mxmxmx/O_C/software/o_c_REV/APP_REFS.ino

// Copyright (c) 2016 Patrick Dowling, 2017 Max Stadler & Tim Churches
//
// Author: Patrick Dowling (pld@gurkenkiste.com)
// Enhancements: Max Stadler and Tim Churches
//
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
// Very simple "reference" voltage app (not so simple any more...)

#include "OC_apps.h"
#include "OC_menus.h"
#include "OC_strings.h"
#include "util/util_settings.h"
#include "OC_autotuner.h"
#include "src/drivers/FreqMeasure/OC_FreqMeasure.h"

// autotune constants:
#define FREQ_MEASURE_TIMEOUT 512
#define ERROR_TIMEOUT (FREQ_MEASURE_TIMEOUT << 0x4)
#define MAX_NUM_PASSES 1500
#define CONVERGE_PASSES 5
// 
static constexpr double kAaboveMidCtoC0 = 0.03716272234383494188492;

//
#ifdef FLIP_180
const uint8_t DAC_CHANNEL_FTM = DAC_CHANNEL_A;
#else
const uint8_t DAC_CHANNEL_FTM = DAC_CHANNEL_D;
#endif

// 
#ifdef BUCHLA_4U
  const float target_multipliers[OCTAVES] = { 1.0f, 2.0f, 4.0f, 8.0f, 16.0f, 32.0f, 64.0f, 128.0f, 256.0f, 512.0f };
#else
  const float target_multipliers[OCTAVES] = { 0.125f, 0.25f, 0.5f, 1.0f, 2.0f, 4.0f, 8.0f, 16.0f, 32.0f, 64.0f };
#endif

#ifdef BUCHLA_SUPPORT
  const float target_multipliers_1V2[OCTAVES] = {
    0.1767766952966368931843f,
    0.3149802624737182976666f,
    0.5612310241546865086093f,
    1.0f,
    1.7817974362806785482150f,
    3.1748021039363991668836f,
    5.6568542494923805818985f,
    10.0793683991589855253324f,
    17.9593927729499718282113f,
    32.0f
  };

  const float target_multipliers_2V0[OCTAVES] = {
    0.3535533905932737863687f,
    0.5f,
    0.7071067811865475727373f,
    1.0f,
    1.4142135623730951454746f,
    2.0f,
    2.8284271247461902909492f,
    4.0f,
    5.6568542494923805818985f,
    8.0f
  };
#endif

const uint8_t NUM_REF_CHANNELS = DAC_CHANNEL_LAST;

enum ReferenceSetting {
  REF_SETTING_OCTAVE,
  REF_SETTING_SEMI,
  REF_SETTING_RANGE,
  REF_SETTING_RATE,
  REF_SETTING_NOTES_OR_BPM,
  REF_SETTING_A_ABOVE_MID_C_INTEGER,
  REF_SETTING_A_ABOVE_MID_C_MANTISSA,
  REF_SETTING_PPQN,
  REF_SETTING_AUTOTUNE,
  REF_SETTING_DUMMY,
  REF_SETTING_LAST
};

enum ChannelPpqn {
  CHANNEL_PPQN_1,
  CHANNEL_PPQN_2,
  CHANNEL_PPQN_4,
  CHANNEL_PPQN_8,
  CHANNEL_PPQN_16,
  CHANNEL_PPQN_24,
  CHANNEL_PPQN_32,
  CHANNEL_PPQN_48,
  CHANNEL_PPQN_64,
  CHANNEL_PPQN_96,
  CHANNEL_PPQN_LAST
};

class ReferenceChannel : public settings::SettingsBase<ReferenceChannel, REF_SETTING_LAST> {
public:

  static constexpr size_t kHistoryDepth = 10;
  
  void Init(DAC_CHANNEL dac_channel) {
    InitDefaults();

    rate_phase_ = 0;
    mod_offset_ = 0;
    last_pitch_ = 0;
    autotuner_ = false;
    autotuner_step_ = OC::DAC_VOLT_0_ARM;
    dac_channel_ = dac_channel;
    auto_DAC_offset_error_ = 0;
    auto_frequency_ = 0;
    auto_last_frequency_ = 0;
    auto_freq_sum_ = 0;
    auto_freq_count_ = 0;
    auto_ready_ = 0;
    ticks_since_last_freq_ = 0;
    auto_next_step_ = false;
    autotune_completed_ = false;
    F_correction_factor_ = 0xFF;
    correction_direction_ = false;
    correction_cnt_positive_ = 0x0;
    correction_cnt_negative_ = 0x0;
    reset_calibration_data();
    update_enabled_settings();
    history_[0].Init(0x0);
  }

  int get_octave() const {
    return values_[REF_SETTING_OCTAVE];
  }

  int get_channel() const {
    return dac_channel_;
  }

  int32_t get_semitone() const {
    return values_[REF_SETTING_SEMI];
  }

  int get_range() const {
    return values_[REF_SETTING_RANGE];
  }

  uint32_t get_rate() const {
    return values_[REF_SETTING_RATE];
  }

  uint8_t get_notes_or_bpm() const {
    return values_[REF_SETTING_NOTES_OR_BPM];
  }

  double get_a_above_mid_c() const {
    double mantissa_divisor = 100.0;
    return static_cast<double>(values_[REF_SETTING_A_ABOVE_MID_C_INTEGER]) + (static_cast<double>(values_[REF_SETTING_A_ABOVE_MID_C_MANTISSA])/mantissa_divisor) ;
  }

  uint8_t get_a_above_mid_c_mantissa() const {
    return values_[REF_SETTING_A_ABOVE_MID_C_MANTISSA];
  }

  ChannelPpqn get_channel_ppqn() const {
    return static_cast<ChannelPpqn>(values_[REF_SETTING_PPQN]);
  }

  uint8_t autotuner_active() {
    return (autotuner_ && autotuner_step_) ? (dac_channel_ + 0x1) : 0x0;
  }

  bool autotuner_completed() {
    return autotune_completed_;
  }

  void autotuner_reset_completed() {
    autotune_completed_ = false;
  }

  bool autotuner_error() {
    return auto_error_;
  }

  uint8_t get_octave_cnt() {
    return octaves_cnt_ + 0x1;
  }

  uint8_t auto_tune_step() {
    return autotuner_step_;
  }

  void autotuner_arm(uint8_t _status) {
    reset_autotuner();
    autotuner_ = _status ? true : false;
  }
  
  void autotuner_run() {     
    autotuner_step_ = autotuner_ ? OC::DAC_VOLT_0_BASELINE : OC::DAC_VOLT_0_ARM;
    if (autotuner_step_ == OC::DAC_VOLT_0_BASELINE)
    // we start, so reset data to defaults:
      OC::DAC::set_default_channel_calibration_data(dac_channel_);
  }

  void auto_reset_step() {
    auto_num_passes_ = 0x0;
    auto_DAC_offset_error_ = 0x0;
    correction_direction_ = false;
    correction_cnt_positive_ = correction_cnt_negative_ = 0x0;
    F_correction_factor_ = 0xFF;
    auto_ready_ = false;
  }

  void reset_autotuner() {
    ticks_since_last_freq_ = 0x0;
    auto_frequency_ = 0x0;
    auto_last_frequency_ = 0x0;
    auto_error_ = 0x0;
    auto_ready_ = 0x0;
    autotuner_ = 0x0;
    autotuner_step_ = 0x0;
    F_correction_factor_ = 0xFF;
    correction_direction_ = false;
    correction_cnt_positive_ = 0x0;
    correction_cnt_negative_ = 0x0;
    octaves_cnt_ = 0x0;
    auto_num_passes_ = 0x0;
    auto_DAC_offset_error_ = 0x0;
    autotune_completed_ = 0x0;
    reset_calibration_data();
  }

  float get_auto_frequency() {
    return auto_frequency_;
  }

  uint8_t _ready() {
     return auto_ready_;
  }

  void reset_calibration_data() {
    
    for (int i = 0; i <= OCTAVES; i++) {
      auto_calibration_data_[i] = 0;
      auto_target_frequencies_[i] = 0.0f;
    }
  }

  uint8_t data_available() {
    return OC::DAC::calibration_data_used(dac_channel_);
  }

  void use_default() {
    OC::DAC::set_default_channel_calibration_data(dac_channel_);
  }

  void use_auto_calibration() {
    OC::DAC::set_auto_channel_calibration_data(dac_channel_);
  }
  
  bool auto_frequency() {

    bool _f_result = false;

    if (ticks_since_last_freq_ > ERROR_TIMEOUT) {
      auto_error_ = true;
    }
    
    if (FreqMeasure.available()) {
      
      auto_freq_sum_ = auto_freq_sum_ + FreqMeasure.read();
      auto_freq_count_ = auto_freq_count_ + 1;

      // take more time as we're converging toward the target frequency
      uint32_t _wait = (F_correction_factor_ == 0x1) ? (FREQ_MEASURE_TIMEOUT << 2) :  (FREQ_MEASURE_TIMEOUT >> 2);
  
      if (ticks_since_last_freq_ > _wait) {

        // store frequency, reset, and poke ui to preempt screensaver:
        auto_frequency_ = FreqMeasure.countToFrequency(auto_freq_sum_ / auto_freq_count_);
        history_[0].Push(auto_frequency_);
        auto_freq_sum_ = 0;
        auto_ready_ = true;
        auto_freq_count_ = 0;
        _f_result = true;
        ticks_since_last_freq_ = 0x0;
        OC::ui._Poke();
        for (auto &sh : history_)
          sh.Update();
      }
    }
    return _f_result;
  }

  void measure_frequency_and_calc_error() {

    switch(autotuner_step_) {

      case OC::DAC_VOLT_0_ARM:
      // do nothing
      break;
      case OC::DAC_VOLT_0_BASELINE:
      // 0V baseline / calibration point: in this case, we don't correct.
      {
        bool _update = auto_frequency();
        if (_update && auto_num_passes_ > kHistoryDepth) { 
          
          auto_last_frequency_ = auto_frequency_;
          float history[kHistoryDepth]; 
          float average = 0.0f;
          // average
          history_->Read(history);
          for (uint8_t i = 0; i < kHistoryDepth; i++)
            average += history[i];
          // ... and derive target frequency at 0V
          auto_frequency_ = (uint32_t) (0.5f + ((auto_frequency_ + average) / (float)(kHistoryDepth + 1))); // 0V 
          // reset step, and proceed:
          auto_reset_step();
          autotuner_step_++;
        }
        else if (_update) 
          auto_num_passes_++;
      }
      break;
      case OC::DAC_VOLT_TARGET_FREQUENCIES: 
      {
        #ifdef BUCHLA_SUPPORT
        
          switch(OC::DAC::get_voltage_scaling(dac_channel_)) {
            
            case VOLTAGE_SCALING_1_2V_PER_OCT: // 1.2V/octave
            auto_target_frequencies_[octaves_cnt_]  =  auto_frequency_ * target_multipliers_1V2[octaves_cnt_];
            break;
            case VOLTAGE_SCALING_2V_PER_OCT: // 2V/octave
            auto_target_frequencies_[octaves_cnt_]  =  auto_frequency_ * target_multipliers_2V0[octaves_cnt_];
            break;
            default: // 1V/octave
            auto_target_frequencies_[octaves_cnt_]  =  auto_frequency_ * target_multipliers[octaves_cnt_]; 
            break;
          }
        #else
          auto_target_frequencies_[octaves_cnt_]  =  auto_frequency_ * target_multipliers[octaves_cnt_]; 
        #endif
        octaves_cnt_++;
        // go to next step, if done:
        if (octaves_cnt_ >= OCTAVES) {
          octaves_cnt_ = 0x0;
          autotuner_step_++;
        }
      }
      break;
      case OC::DAC_VOLT_3m:
      case OC::DAC_VOLT_2m:
      case OC::DAC_VOLT_1m: 
      case OC::DAC_VOLT_0:
      case OC::DAC_VOLT_1:
      case OC::DAC_VOLT_2:
      case OC::DAC_VOLT_3:
      case OC::DAC_VOLT_4:
      case OC::DAC_VOLT_5:
      case OC::DAC_VOLT_6:
      { 
        bool _update = auto_frequency();
        
        if (_update && (auto_num_passes_ > MAX_NUM_PASSES)) {  
          /* target frequency reached */
          
          if ((autotuner_step_ > OC::DAC_VOLT_2m) && (auto_last_frequency_ * 1.25f > auto_frequency_))
              auto_error_ = true; // throw error, if things don't seem to double ...
          // average:
          float history[kHistoryDepth]; 
          float average = 0.0f;
          history_->Read(history);
          for (uint8_t i = 0; i < kHistoryDepth; i++)
            average += history[i];
          // store last frequency:
           auto_last_frequency_  = ((auto_frequency_ + average) / (float)(kHistoryDepth + 1));
          // and DAC correction value:
          auto_calibration_data_[autotuner_step_ - OC::DAC_VOLT_3m] = auto_DAC_offset_error_;
          // and reset step:
          auto_reset_step();
          autotuner_step_++; 
        }
        // 
        else if (_update) {

          // count passes
          auto_num_passes_++;
          // and correct frequency
          if (auto_target_frequencies_[autotuner_step_ - OC::DAC_VOLT_3m] > auto_frequency_) {
            // update correction factor?
            if (!correction_direction_)
              F_correction_factor_ = (F_correction_factor_ >> 1) | 1u;
            correction_direction_ = true;
            
            auto_DAC_offset_error_ += F_correction_factor_;
            // we're converging -- count passes, so we can stop after x attempts:
            if (F_correction_factor_ == 0x1)
              correction_cnt_positive_++;
          }
          else if (auto_target_frequencies_[autotuner_step_ - OC::DAC_VOLT_3m] < auto_frequency_) {
            // update correction factor?
            if (correction_direction_)
              F_correction_factor_ = (F_correction_factor_ >> 1) | 1u;
            correction_direction_ = false;
            
            auto_DAC_offset_error_ -= F_correction_factor_;
            // we're converging -- count passes, so we can stop after x attempts:
            if (F_correction_factor_ == 0x1)
              correction_cnt_negative_++;
          }

          // approaching target? if so, go to next step.
          if (correction_cnt_positive_ > CONVERGE_PASSES && correction_cnt_negative_ > CONVERGE_PASSES)
            auto_num_passes_ = MAX_NUM_PASSES << 1;
        }
      }
      break;
      case OC::AUTO_CALIBRATION_STEP_LAST:
      // step through the octaves:
      if (ticks_since_last_freq_ > 2000) {
        int32_t new_auto_calibration_point = OC::calibration_data.dac.calibrated_octaves[dac_channel_][octaves_cnt_] + auto_calibration_data_[octaves_cnt_];
        // write to DAC and update data
        if (new_auto_calibration_point >= 65536 || new_auto_calibration_point < 0) {
          auto_error_ = true;
          autotuner_step_++;
        }
        else {
          OC::DAC::set(dac_channel_, new_auto_calibration_point);
          OC::DAC::update_auto_channel_calibration_data(dac_channel_, octaves_cnt_, new_auto_calibration_point);
          ticks_since_last_freq_ = 0x0;
          octaves_cnt_++;
        }
      }
      // then stop ... 
      if (octaves_cnt_ > OCTAVES) { 
        autotune_completed_ = true;
        // and point to auto data ...
        OC::DAC::set_auto_channel_calibration_data(dac_channel_);
        autotuner_step_++;
      }
      break;
      default:
      autotuner_step_ = OC::DAC_VOLT_0_ARM;
      autotuner_ = 0x0;
      break;
    }
  }
  
  void autotune_updateDAC() {

    switch(autotuner_step_) {

      case OC::DAC_VOLT_0_ARM: 
      {
        F_correction_factor_ = 0x1; // don't go so fast
        auto_frequency();
        OC::DAC::set(dac_channel_, OC::calibration_data.dac.calibrated_octaves[dac_channel_][OC::DAC::kOctaveZero]);
      }
      break;
      case OC::DAC_VOLT_0_BASELINE:
      // set DAC to 0.000V, default calibration:
      OC::DAC::set(dac_channel_, OC::calibration_data.dac.calibrated_octaves[dac_channel_][OC::DAC::kOctaveZero]);
      break;
      case OC::DAC_VOLT_TARGET_FREQUENCIES:
      case OC::AUTO_CALIBRATION_STEP_LAST:
      // do nothing
      break;
      default: 
      // set DAC to calibration point + error
      {
        int32_t _default_calibration_point = OC::calibration_data.dac.calibrated_octaves[dac_channel_][autotuner_step_ - OC::DAC_VOLT_3m];
        OC::DAC::set(dac_channel_, _default_calibration_point + auto_DAC_offset_error_);
      }
      break;
    }
  }
 
  void Update() {

    if (autotuner_) {
      autotune_updateDAC();
      ticks_since_last_freq_++;
      return;
    }

    int octave = get_octave();
    int range = get_range();
    if (range) {
      rate_phase_ += OC_CORE_TIMER_RATE;
      if (rate_phase_ >= get_rate() * 1000000UL) {
        rate_phase_ = 0;
        mod_offset_ = 1 - mod_offset_;
      }
      octave += mod_offset_ * range;
    } else {
      rate_phase_ = 0;
      mod_offset_ = 0;
    }

    int32_t semitone = get_semitone();
    OC::DAC::set(dac_channel_, OC::DAC::semitone_to_scaled_voltage_dac(dac_channel_, semitone, octave, OC::DAC::get_voltage_scaling(dac_channel_)));
    last_pitch_ = (semitone + octave * 12) << 7;       
  }

  int num_enabled_settings() const {
    return num_enabled_settings_;
  }

  ReferenceSetting enabled_setting_at(int index) const {
    return enabled_settings_[index];
  }

  void update_enabled_settings() {
    ReferenceSetting *settings = enabled_settings_;
    *settings++ = REF_SETTING_OCTAVE;
    *settings++ = REF_SETTING_SEMI;
    *settings++ = REF_SETTING_RANGE;
    *settings++ = REF_SETTING_RATE;
    *settings++ = REF_SETTING_AUTOTUNE;
    //*settings++ = REF_SETTING_AUTOTUNE_ERROR;

    if (DAC_CHANNEL_FTM == dac_channel_) {
      *settings++ = REF_SETTING_NOTES_OR_BPM;
      *settings++ = REF_SETTING_A_ABOVE_MID_C_INTEGER;
      *settings++ = REF_SETTING_A_ABOVE_MID_C_MANTISSA;
      *settings++ = REF_SETTING_PPQN;
    }
    else {
      *settings++ = REF_SETTING_DUMMY;
      *settings++ = REF_SETTING_DUMMY;
    }
    
     num_enabled_settings_ = settings - enabled_settings_;
  }

  void RenderScreensaver(weegfx::coord_t start_x, uint8_t chan) const;

private:
  uint32_t rate_phase_;
  int mod_offset_;
  int32_t last_pitch_;
  bool autotuner_;
  uint8_t autotuner_step_;
  int32_t auto_DAC_offset_error_;
  float auto_frequency_;
  float auto_target_frequencies_[OCTAVES + 1];
  int16_t auto_calibration_data_[OCTAVES + 1];
  float auto_last_frequency_;
  bool auto_next_step_;
  bool auto_error_;
  bool auto_ready_;
  bool autotune_completed_;
  uint32_t auto_freq_sum_;
  uint32_t auto_freq_count_;
  uint32_t ticks_since_last_freq_;
  uint32_t auto_num_passes_;
  uint16_t F_correction_factor_;
  bool correction_direction_;
  int16_t correction_cnt_positive_;
  int16_t correction_cnt_negative_;
  int16_t octaves_cnt_;
  DAC_CHANNEL dac_channel_;

  OC::vfx::ScrollingHistory<float, kHistoryDepth> history_[0x1];

  int num_enabled_settings_;
  ReferenceSetting enabled_settings_[REF_SETTING_LAST];
};

const char* const notes_or_bpm[2] = {
 "notes",  "bpm", 
};

const char* const ppqn_labels[10] = {
 " 1",  " 2", " 4", " 8", "16", "24", "32", "48", "64", "96",  
};

const char* const error[] = {
  "0.050", "0.125", "0.250", "0.500", "1.000", "2.000", "4.000"
};

SETTINGS_DECLARE(ReferenceChannel, REF_SETTING_LAST) {
  #ifdef BUCHLA_4U
  { 0, 0, 9, "Octave", nullptr, settings::STORAGE_TYPE_I8 },
  #elif defined(VOR) 
  {0, 0, 10, "Octave", nullptr, settings::STORAGE_TYPE_I8 },
  #else
  { 0, -3, 6, "Octave", nullptr, settings::STORAGE_TYPE_I8 },
  #endif
  { 0, 0, 11, "Semitone", OC::Strings::note_names_unpadded, settings::STORAGE_TYPE_U8 },
  { 0, -3, 3, "Mod range oct", nullptr, settings::STORAGE_TYPE_U8 },
  { 0, 0, 30, "Mod rate (s)", nullptr, settings::STORAGE_TYPE_U8 },
  { 0, 0, 1, "Notes/BPM :", notes_or_bpm, settings::STORAGE_TYPE_U8 },
  { 440, 400, 480, "A above mid C", nullptr, settings::STORAGE_TYPE_U16 },
  { 0, 0, 99, " > mantissa", nullptr, settings::STORAGE_TYPE_U8 },
  { CHANNEL_PPQN_4, CHANNEL_PPQN_1, CHANNEL_PPQN_LAST - 1, "> ppqn", ppqn_labels, settings::STORAGE_TYPE_U8 },
  { 0, 0, 0, "--> autotune", NULL, settings::STORAGE_TYPE_U8 },
  { 0, 0, 0, "-", NULL, settings::STORAGE_TYPE_U8 } // dummy
};

class ReferencesApp {
public:
  ReferencesApp() { }
  
  OC::Autotuner<ReferenceChannel> autotuner;

  void Init() {
    int dac_channel = DAC_CHANNEL_A;
    for (auto &channel : channels_)
      channel.Init(static_cast<DAC_CHANNEL>(dac_channel++));

    ui.selected_channel = DAC_CHANNEL_FTM;
    ui.cursor.Init(0, channels_[DAC_CHANNEL_FTM].num_enabled_settings() - 1);

    freq_sum_ = 0;
    freq_count_ = 0;
    frequency_ = 0;
    autotuner.Init();
  }

  void ISR() {
      
    for (auto &channel : channels_)
      channel.Update();

    uint8_t _autotuner_active_channel = 0x0;
    for (auto &channel : channels_)
       _autotuner_active_channel += channel.autotuner_active();

    if (_autotuner_active_channel) {
      channels_[_autotuner_active_channel - 0x1].measure_frequency_and_calc_error();
      return;
    }
    else if (FreqMeasure.available()) {
      // average several readings together
      freq_sum_ = freq_sum_ + FreqMeasure.read();
      freq_count_ = freq_count_ + 1;
      
      if (milliseconds_since_last_freq_ > 750) {
        frequency_ = FreqMeasure.countToFrequency(freq_sum_ / freq_count_);
        freq_sum_ = 0;
        freq_count_ = 0;
        milliseconds_since_last_freq_ = 0;
       }
     } else if (milliseconds_since_last_freq_ > 100000) {
      frequency_ = 0.0f;
     }
  }

  ReferenceChannel &selected_channel() {
    return channels_[ui.selected_channel];
  }

  struct {
    int selected_channel;
    menu::ScreenCursor<menu::kScreenLines> cursor;
  } ui;

  ReferenceChannel channels_[DAC_CHANNEL_LAST];

  float get_frequency( ) {
    return(frequency_) ;
  }

  float get_ppqn() {
    float ppqn_ = 4.0 ;
    switch(channels_[DAC_CHANNEL_FTM].get_channel_ppqn()){
      case CHANNEL_PPQN_1:
        ppqn_ = 1.0;
        break;
      case CHANNEL_PPQN_2:
        ppqn_ = 2.0;
        break;
      case CHANNEL_PPQN_4:
        ppqn_ = 4.0;
        break;
      case CHANNEL_PPQN_8:
        ppqn_ = 8.0;
        break;
      case CHANNEL_PPQN_16:
        ppqn_ = 16.0;
        break;
      case CHANNEL_PPQN_24:
        ppqn_ = 24.0;
        break;
      case CHANNEL_PPQN_32:
        ppqn_ = 32.0;
        break;
      case CHANNEL_PPQN_48:
        ppqn_ = 48.0;
        break;
      case CHANNEL_PPQN_64:
        ppqn_ = 64.0;
        break;
      case CHANNEL_PPQN_96:
        ppqn_ = 96.0;
        break;
      default:
        ppqn_ = 8.0 ;
        break;
    }
    return(ppqn_);
  }

  float get_bpm( ) {
    return((60.0 * frequency_)/get_ppqn()) ;
  }

  bool get_notes_or_bpm( ) {
    return(static_cast<bool>(channels_[DAC_CHANNEL_FTM].get_notes_or_bpm())) ;
  }

  float get_C0_freq() {
    return(static_cast<float>(channels_[DAC_CHANNEL_FTM].get_a_above_mid_c() * kAaboveMidCtoC0));
  }

private:
  double freq_sum_;
  uint32_t freq_count_;
  float frequency_ ;
  elapsedMillis milliseconds_since_last_freq_;
};

ReferencesApp references_app;

// App stubs
void REFS_init() {
  references_app.Init();
}

size_t REFS_storageSize() {
  return NUM_REF_CHANNELS * ReferenceChannel::storageSize();
}

size_t REFS_save(void *storage) {
  size_t used = 0;
  for (size_t i = 0; i < NUM_REF_CHANNELS; ++i) {
    used += references_app.channels_[i].Save(static_cast<char*>(storage) + used);
  }
  return used;
}

size_t REFS_restore(const void *storage) {
  size_t used = 0;
  for (size_t i = 0; i < NUM_REF_CHANNELS; ++i) {
    used += references_app.channels_[i].Restore(static_cast<const char*>(storage) + used);
    references_app.channels_[i].update_enabled_settings();
  }
  references_app.ui.cursor.AdjustEnd(references_app.channels_[0].num_enabled_settings() - 1);
  return used;
}

void REFS_isr() {
  return references_app.ISR();
}

void REFS_handleAppEvent(OC::AppEvent event) {
  switch (event) {
    case OC::APP_EVENT_RESUME:
      references_app.ui.cursor.set_editing(false);
      FreqMeasure.begin();
      references_app.autotuner.Close();
      break;
    case OC::APP_EVENT_SUSPEND:
    case OC::APP_EVENT_SCREENSAVER_ON:
    case OC::APP_EVENT_SCREENSAVER_OFF:
      for (size_t i = 0; i < NUM_REF_CHANNELS; ++i)
        references_app.channels_[i].reset_autotuner();
      break;
  }
}

void REFS_loop() {
}

void REFS_menu() {
  menu::QuadTitleBar::Draw();
  for (uint_fast8_t i = 0; i < NUM_REF_CHANNELS; ++i) {
    menu::QuadTitleBar::SetColumn(i);
    graphics.print((char)('A' + i));
  }
  menu::QuadTitleBar::Selected(references_app.ui.selected_channel);

  const auto &channel = references_app.selected_channel();
  menu::SettingsList<menu::kScreenLines, 0, menu::kDefaultValueX> settings_list(references_app.ui.cursor);
  menu::SettingsListItem list_item;

  while (settings_list.available()) {
    const int setting = 
      channel.enabled_setting_at(settings_list.Next(list_item));
    const int value = channel.get_value(setting);
    const settings::value_attr &attr = ReferenceChannel::value_attr(setting);

    switch (setting) {
      case REF_SETTING_AUTOTUNE:
      case REF_SETTING_DUMMY:
         list_item.DrawNoValue<false>(value, attr);
      break;
      default:
        list_item.DrawDefault(value, attr);
      break;
    }
  }
  // autotuner ...
  if (references_app.autotuner.active())
    references_app.autotuner.Draw();
}

void print_voltage(int octave, int fraction) {
  graphics.printf("%01d", octave);
  graphics.movePrintPos(-1, 0); graphics.print('.');
  graphics.movePrintPos(-2, 0); graphics.printf("%03d", fraction);
}

void ReferenceChannel::RenderScreensaver(weegfx::coord_t start_x, uint8_t chan) const {

  // Mostly borrowed from QQ

  weegfx::coord_t x = start_x + 26;
  weegfx::coord_t y = 34 ; // was 60
  // for (int i = 0; i < 5 ; ++i, y -= 4) // was i < 12
    graphics.setPixel(x, y);

  int32_t pitch = last_pitch_ ;
  int32_t unscaled_pitch = last_pitch_ ;

  #ifdef BUCHLA_SUPPORT
    switch (OC::DAC::get_voltage_scaling(chan)) {
      
        case VOLTAGE_SCALING_1_2V_PER_OCT: // 1.2V/oct
            pitch = (pitch * 19661) >> 14 ;
            break;
        case VOLTAGE_SCALING_2V_PER_OCT: // 2V/oct
            pitch = pitch << 1 ;
            break;
        default: // 1V/oct
            break;
     }
   #endif 

  pitch += (OC::DAC::kOctaveZero * 12) << 7;
  unscaled_pitch += (OC::DAC::kOctaveZero * 12) << 7;

  
  CONSTRAIN(pitch, 0, 120 << 7);

  int32_t octave = pitch / (12 << 7);
  int32_t unscaled_octave = unscaled_pitch / (12 << 7);
  pitch -= (octave * 12 << 7);
  unscaled_pitch -= (unscaled_octave * 12 << 7);
  int semitone = pitch >> 7;
  int unscaled_semitone = unscaled_pitch >> 7;

  y = 34 - unscaled_semitone * 2; // was 60, multiplier was 4
  if (unscaled_semitone < 6)
    graphics.setPrintPos(start_x + menu::kIndentDx, y - 7);
  else
    graphics.setPrintPos(start_x + menu::kIndentDx, y);
  graphics.print(OC::Strings::note_names_unpadded[unscaled_semitone]);

  graphics.drawHLine(start_x + 16, y, 8);
  graphics.drawBitmap8(start_x + 28, 34 - unscaled_octave * 2 - 1, OC::kBitmapLoopMarkerW, OC::bitmap_loop_markers_8 + OC::kBitmapLoopMarkerW); // was 60

  #ifdef BUCHLA_SUPPORT
    // Try and round to 3 digits
    switch (OC::DAC::get_voltage_scaling(chan)) {
      
        case VOLTAGE_SCALING_1_2V_PER_OCT: // 1.2V/oct
            semitone = (semitone * 10000 + 40) / 100;
            break;
        case VOLTAGE_SCALING_2V_PER_OCT: // 2V/oct
        default: // 1V/oct
            semitone = (semitone * 10000 + 50) / 120;
            break;
     }
   #else
    semitone = (semitone * 10000 + 50) / 120;
   #endif
   
  semitone %= 1000;
  octave -= OC::DAC::kOctaveZero;


  // We want [sign]d.ddd = 6 chars in 32px space; with the current font width
  // of 6px that's too tight, so squeeze in the mini minus...
  y = menu::kTextDy;
  graphics.setPrintPos(start_x + menu::kIndentDx, y);
  if (octave >= 0) {
    print_voltage(octave, semitone);
  } else {
    graphics.drawHLine(start_x, y + 3, 2);
    if (semitone)
      print_voltage(-octave - 1, 1000 - semitone);
    else
      print_voltage(-octave, 0);
  }
}

void REFS_screensaver() {
  references_app.channels_[0].RenderScreensaver( 0, 0);
  references_app.channels_[1].RenderScreensaver(32, 1);
  references_app.channels_[2].RenderScreensaver(64, 2);
  references_app.channels_[3].RenderScreensaver(96, 3);
  graphics.setPrintPos(2, 44);

  float frequency_ = references_app.get_frequency() ;
  float c0_freq_ = references_app.get_C0_freq() ;
  float bpm_ = (60.0 * frequency_)/references_app.get_ppqn() ;

  int32_t freq_decicents_deviation_ = round(12000.0 * log2f(frequency_ / c0_freq_)) + 500;
  int8_t freq_octave_ = -2 + ((freq_decicents_deviation_)/ 12000) ;
  int8_t freq_note_ = (freq_decicents_deviation_ - ((freq_octave_ + 2) * 12000)) / 1000;
  int32_t freq_decicents_residual_ = ((freq_decicents_deviation_ - ((freq_octave_ - 1) * 12000)) % 1000) - 500;

  if (frequency_ > 0.0) {
    #ifdef FLIP_180
    graphics.printf("TR1 %7.3f Hz", frequency_);
    #else
    graphics.printf("TR4 %7.3f Hz", frequency_);
    #endif
    graphics.setPrintPos(2, 56);
    if (references_app.get_notes_or_bpm()) {
      graphics.printf("%7.2f bpm %2.0fppqn", bpm_, references_app.get_ppqn());
    } else if(frequency_ >= c0_freq_) {
      graphics.printf("%+i %s %+7.1fc", freq_octave_, OC::Strings::note_names[freq_note_], freq_decicents_residual_ / 10.0) ;
    }
  } else {
    graphics.print("TR4 no input") ;
  }
}

void REFS_handleButtonEvent(const UI::Event &event) {

  if (references_app.autotuner.active()) {
    references_app.autotuner.HandleButtonEvent(event);
    return;
  }
  
  if (OC::CONTROL_BUTTON_R == event.control) {

    auto &selected_channel = references_app.selected_channel();
    switch (selected_channel.enabled_setting_at(references_app.ui.cursor.cursor_pos())) {
      case REF_SETTING_AUTOTUNE:
      references_app.autotuner.Open(&selected_channel);
      break;
      case REF_SETTING_DUMMY:
      break;
      default:
      references_app.ui.cursor.toggle_editing();
      break;
    }
  }
}

void REFS_handleEncoderEvent(const UI::Event &event) {

  if (references_app.autotuner.active()) {
    references_app.autotuner.HandleEncoderEvent(event);
    return;
  }
  
  if (OC::CONTROL_ENCODER_L == event.control) {
    
    int previous = references_app.selected_channel().num_enabled_settings();
    int selected = references_app.ui.selected_channel + event.value;
    CONSTRAIN(selected, 0, NUM_REF_CHANNELS - 0x1);
    references_app.ui.selected_channel = selected;

    // hack -- deal w/ menu items / channels
    if ((references_app.ui.cursor.cursor_pos() > 4) && (previous > references_app.selected_channel().num_enabled_settings())) {
      references_app.ui.cursor.Init(0, 0);
      references_app.ui.cursor.AdjustEnd(references_app.selected_channel().num_enabled_settings() - 1);
    }
    else
      references_app.ui.cursor.AdjustEnd(references_app.selected_channel().num_enabled_settings() - 1);
  } else if (OC::CONTROL_ENCODER_R == event.control) {
    if (references_app.ui.cursor.editing()) {
        auto &selected_channel = references_app.selected_channel();
        ReferenceSetting setting = selected_channel.enabled_setting_at(references_app.ui.cursor.cursor_pos());
        if (setting == REF_SETTING_DUMMY) 
          references_app.ui.cursor.set_editing(false);
        selected_channel.change_value(setting, event.value);
        selected_channel.update_enabled_settings();
    } else {
      references_app.ui.cursor.Scroll(event.value);
    }
  }
}
