mxmxmx/O_C/software/o_c_REV/APP_CHORDS.ino

// Copyright (c) 2015, 2016, 2017 Patrick Dowling, Tim Churches, Max Stadler
//
// Initial app implementation: Patrick Dowling (pld@gurkenkiste.com)
// Modifications by: Tim Churches (tim.churches@gmail.com)
// Yet more Modifications by: mxmxmx 
//
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
// Quad quantizer app, based around the the quantizer/scales implementation from
// from Braids by Olivier Gillet (see braids_quantizer.h/cc et al.). It has since
// grown a little bit...

#include "OC_apps.h"
#include "util/util_settings.h"
#include "util/util_trigger_delay.h"
#include "braids_quantizer.h"
#include "braids_quantizer_scales.h"
#include "OC_menus.h"
#include "OC_scales.h"
#include "OC_scale_edit.h"
#include "OC_strings.h"
#include "OC_chords.h"
#include "OC_chords_edit.h"
#include "OC_input_map.h"
#include "OC_input_maps.h"

enum CHORDS_SETTINGS {
  CHORDS_SETTING_SCALE,
  CHORDS_SETTING_ROOT,
  CHORDS_SETTING_PROGRESSION,
  CHORDS_SETTING_MASK,
  CHORDS_SETTING_CV_SOURCE,
  CHORDS_SETTING_CHORDS_ADVANCE_TRIGGER_SOURCE,
  CHORDS_SETTING_PLAYMODES,
  CHORDS_SETTING_DIRECTION,
  CHORDS_SETTING_BROWNIAN_PROBABILITY,
  CHORDS_SETTING_TRIGGER_DELAY,
  CHORDS_SETTING_TRANSPOSE,
  CHORDS_SETTING_OCTAVE,
  CHORDS_SETTING_CHORD_SLOT,
  CHORDS_SETTING_NUM_CHORDS_0,
  CHORDS_SETTING_NUM_CHORDS_1,
  CHORDS_SETTING_NUM_CHORDS_2,
  CHORDS_SETTING_NUM_CHORDS_3,
  CHORDS_SETTING_CHORD_EDIT,
  // CV sources
  CHORDS_SETTING_ROOT_CV,
  CHORDS_SETTING_MASK_CV,
  CHORDS_SETTING_TRANSPOSE_CV,
  CHORDS_SETTING_OCTAVE_CV,
  CHORDS_SETTING_QUALITY_CV,
  CHORDS_SETTING_VOICING_CV,
  CHORDS_SETTING_INVERSION_CV,
  CHORDS_SETTING_PROGRESSION_CV,
  CHORDS_SETTING_DIRECTION_CV,
  CHORDS_SETTING_BROWNIAN_CV,
  CHORDS_SETTING_NUM_CHORDS_CV,
  CHORDS_SETTING_DUMMY,
  CHORDS_SETTING_MORE_DUMMY,
  CHORDS_SETTING_LAST
};

enum CHORDS_CV_SOURCES {
  CHORDS_CV_SOURCE_CV1,
  CHORDS_CV_SOURCE_CV2,
  CHORDS_CV_SOURCE_CV3,
  CHORDS_CV_SOURCE_CV4,
  CHORDS_CV_SOURCE_LAST
};

enum CHORDS_ADVANCE_TRIGGER_SOURCE {
  CHORDS_ADVANCE_TRIGGER_SOURCE_TR1,
  CHORDS_ADVANCE_TRIGGER_SOURCE_TR2,
  CHORDS_ADVANCE_TRIGGER_SOURCE_LAST
};

enum CHORDS_CV_DESTINATIONS {
  CHORDS_CV_DEST_NONE,
  CHORDS_CV_DEST_ROOT,
  CHORDS_CV_DEST_OCTAVE,
  CHORDS_CV_DEST_TRANSPOSE,
  CHORDS_CV_DEST_MASK,
  CHORDS_CV_DEST_LAST
};

enum CHORDS_MENU_PAGES {
  MENU_PARAMETERS,
  MENU_CV_MAPPING,
  MENU_PAGES_LAST  
};

enum CHORDS_PLAYMODES {
  _NONE,
  _SEQ1,
  _SEQ2,
  _SEQ3,
  _TR1,
  _TR2,
  _TR3,
  _SH1,
  _SH2,
  _SH3,
  _SH4,
  _CV1,
  _CV2,
  _CV3,
  _CV4,
  CHORDS_PLAYMODES_LAST
};

enum CHORDS_DIRECTIONS {
  CHORDS_FORWARD,
  CHORDS_REVERSE,
  CHORDS_PENDULUM1,
  CHORDS_PENDULUM2,
  CHORDS_RANDOM,
  CHORDS_BROWNIAN,
  CHORDS_DIRECTIONS_LAST
};

class Chords : public settings::SettingsBase<Chords, CHORDS_SETTING_LAST> {
public:
  
  int get_scale(uint8_t selected_scale_slot_) const {
    return values_[CHORDS_SETTING_SCALE];
  } 

  void set_scale(int scale) {

    if (scale != get_scale(DUMMY)) {
      const OC::Scale &scale_def = OC::Scales::GetScale(scale);
      uint16_t mask = get_mask();
      if (0 == (mask & ~(0xffff << scale_def.num_notes)))
        mask |= 0x1;
      apply_value(CHORDS_SETTING_MASK, mask);
      apply_value(CHORDS_SETTING_SCALE, scale);
    }
  }
  
  // dummy
  int get_scale_select() const {
    return 0;
  }

  // dummy
  void set_scale_at_slot(int scale, uint16_t mask, int root, int transpose, uint8_t scale_slot) {
    
  }

  // dummy
  int get_transpose(uint8_t DUMMY) const {
    return 0;
  }

  bool octave_toggle() {
    _octave_toggle = (~_octave_toggle) & 1u;
    return _octave_toggle;
  }
  
  bool poke_octave_toggle() const {
    return _octave_toggle;
  }
  
  int get_progression() const {
    return values_[CHORDS_SETTING_PROGRESSION];
  }

  int get_progression_cv() const {
    return values_[CHORDS_SETTING_PROGRESSION_CV];
  }
  
  int get_active_progression() const {
    return active_progression_;
  }

  int get_chord_slot() const {
    return values_[CHORDS_SETTING_CHORD_SLOT];
  }

  void set_chord_slot(int8_t slot) {
    apply_value(CHORDS_SETTING_CHORD_SLOT, slot);
  }

  int get_num_chords(uint8_t progression) const {

     int len = 0x0;
     switch (progression) {
      
        case 0:
          len = values_[CHORDS_SETTING_NUM_CHORDS_0];
        break;
        case 1:
          len = values_[CHORDS_SETTING_NUM_CHORDS_1];
        break;
        case 2:
          len = values_[CHORDS_SETTING_NUM_CHORDS_2];
        break;
        case 3:
          len =  values_[CHORDS_SETTING_NUM_CHORDS_3];
        break;
        default:
        break;
    }
    return len;
  }

  void set_num_chords(int8_t num_chords, uint8_t progression) {

    // set progression length:
    switch (progression) {
      case 0:
      apply_value(CHORDS_SETTING_NUM_CHORDS_0, num_chords);
      break;
      case 1:
      apply_value(CHORDS_SETTING_NUM_CHORDS_1, num_chords);
      break;
      case 2:
      apply_value(CHORDS_SETTING_NUM_CHORDS_2, num_chords);
      break;
      case 3:
      apply_value(CHORDS_SETTING_NUM_CHORDS_3, num_chords);
      break;
      default:
      break;
    }
  }

  int get_num_chords_cv() const {
    return values_[CHORDS_SETTING_NUM_CHORDS_CV];
  }

  int active_chord() const {
    return active_chord_;
  }

  int get_playmode() const {
    return values_[CHORDS_SETTING_PLAYMODES];
  }

  int get_direction() const {
    return values_[CHORDS_SETTING_DIRECTION];
  }

  uint8_t get_direction_cv() const {
    return values_[CHORDS_SETTING_DIRECTION_CV];
  }

  uint8_t get_brownian_probability() const {
    return values_[CHORDS_SETTING_BROWNIAN_PROBABILITY];
  }

  int8_t get_brownian_probability_cv() const {
    return values_[CHORDS_SETTING_BROWNIAN_CV];
  }
  
  int get_root() const {
    return values_[CHORDS_SETTING_ROOT];
  }

  int get_root(uint8_t DUMMY) const {
    return 0x0;
  }

  uint8_t get_root_cv() const {
    return values_[CHORDS_SETTING_ROOT_CV];
  }
  
  int get_display_num_chords() const {
    return display_num_chords_;
  }

  uint16_t get_mask() const {
    return values_[CHORDS_SETTING_MASK];
  }

  uint16_t get_rotated_mask() const {
    return last_mask_;
  }

  uint8_t get_mask_cv() const {
    return values_[CHORDS_SETTING_MASK_CV];
  }

  int16_t get_cv_source() const {
    return values_[CHORDS_SETTING_CV_SOURCE];
  }

  int8_t get_chords_trigger_source() const {
    return values_[CHORDS_SETTING_CHORDS_ADVANCE_TRIGGER_SOURCE];
  }

  uint16_t get_trigger_delay() const {
    return values_[CHORDS_SETTING_TRIGGER_DELAY];
  }

  int get_transpose() const {
    return values_[CHORDS_SETTING_TRANSPOSE];
  }

  uint8_t get_transpose_cv() const {
    return values_[CHORDS_SETTING_TRANSPOSE_CV];
  }

  int get_octave() const {
    return values_[CHORDS_SETTING_OCTAVE];
  }

  uint8_t get_octave_cv() const {
    return values_[CHORDS_SETTING_OCTAVE_CV];
  }

  uint8_t get_quality_cv() const {
    return values_[CHORDS_SETTING_QUALITY_CV];
  }

  uint8_t get_inversion_cv() const {
    return values_[CHORDS_SETTING_INVERSION_CV];
  }

  uint8_t get_voicing_cv() const {
    return values_[CHORDS_SETTING_VOICING_CV];
  }

  uint8_t clockState() const {
    return clock_display_.getState();
  }

  uint8_t get_menu_page() const {
    return menu_page_;  
  }

  void set_menu_page(uint8_t _menu_page) {
    menu_page_ = _menu_page;  
  }

  void update_inputmap(int num_slots, uint8_t range) {
    input_map_.Configure(OC::InputMaps::GetInputMap(num_slots), range);
  }

  void clear_CV_mapping() {
    // clear all ... 
    apply_value(CHORDS_SETTING_ROOT_CV, 0);
    apply_value(CHORDS_SETTING_MASK_CV, 0);
    apply_value(CHORDS_SETTING_TRANSPOSE_CV, 0);
    apply_value(CHORDS_SETTING_OCTAVE_CV, 0);
    apply_value(CHORDS_SETTING_QUALITY_CV, 0);
    apply_value(CHORDS_SETTING_VOICING_CV, 0); 
    apply_value(CHORDS_SETTING_INVERSION_CV, 0);
    apply_value(CHORDS_SETTING_BROWNIAN_CV, 0);  
    apply_value(CHORDS_SETTING_DIRECTION_CV, 0);
    apply_value(CHORDS_SETTING_PROGRESSION_CV, 0);   
    apply_value(CHORDS_SETTING_NUM_CHORDS_CV, 0); 
  }
  
  void Init() {
    
    InitDefaults();
    menu_page_ = PARAMETERS;
    apply_value(CHORDS_SETTING_CV_SOURCE, 0x0);
    set_scale(OC::Scales::SCALE_SEMI);
    force_update_ = true;
    _octave_toggle = false;
    last_scale_= -1;
    last_mask_ = 0;
    last_sample_ = 0;
    chord_advance_last_ = true;
    progression_advance_last_ = true;
    active_chord_ = 0;
    chord_repeat_ = false;
    progression_cnt_ = 0;
    active_progression_ = 0;
    playmode_last_ = 0;
    progression_last_ = 0;
    progression_EoP_ = 0;
    num_chords_last_ = 0;
    chords_direction_ = true;
    display_num_chords_ = 0x1;
   
    trigger_delay_.Init();
    input_map_.Init();
    quantizer_.Init();
    chords_.Init();
    update_scale(true, false);
    clock_display_.Init();
    update_enabled_settings();
  }

  void force_update() {
    //force_update_ = true;
  }

  int8_t _clock(uint8_t sequence_length, uint8_t sequence_count, uint8_t sequence_max, bool _reset) {

        int8_t EoP = 0x0, _clk_cnt, _direction;
        bool reset = !digitalReadFast(TR4) | _reset;
        
        _clk_cnt = active_chord_;
        _direction = get_direction();

        if (get_direction_cv()) {
           _direction += (OC::ADC::value(static_cast<ADC_CHANNEL>(get_direction_cv() - 1)) + 255) >> 9;
           CONSTRAIN(_direction, 0, CHORDS_DIRECTIONS_LAST - 0x1);
        }
        
        switch (_direction) {

          case CHORDS_FORWARD:
          {
            _clk_cnt++;
            if (reset)
              _clk_cnt = 0x0;
            // end of sequence?  
            else if (_clk_cnt > sequence_length)
              _clk_cnt = 0x0;
            else if (_clk_cnt == sequence_length)
               EoP = 0x1;  
          }
          break;
          case CHORDS_REVERSE:
          {
            _clk_cnt--;
            if (reset)
              _clk_cnt = sequence_length;
            // end of sequence? 
            else if (_clk_cnt < 0) 
              _clk_cnt = sequence_length;
            else if (!_clk_cnt)  
               EoP = 0x1;
          }
          break;
          case CHORDS_PENDULUM1:
          case CHORDS_BROWNIAN:
          if (CHORDS_BROWNIAN == get_direction()) {
            // Compare Brownian probability and reverse direction if needed
            int16_t brown_prb = get_brownian_probability();

            if (get_brownian_probability_cv()) {
              brown_prb += (OC::ADC::value(static_cast<ADC_CHANNEL>(get_brownian_probability_cv() - 1)) + 8) >> 3;
              CONSTRAIN(brown_prb, 0, 256);
            }
            if (random(0,256) < brown_prb) 
              chords_direction_ = !chords_direction_; 
          }
          {
            if (chords_direction_) {
              _clk_cnt++;  
              if (reset)
                _clk_cnt = 0x0;
              else if (_clk_cnt >= sequence_length) {
                
                if (sequence_count >= sequence_max) {
                  chords_direction_ = false;
                  _clk_cnt = sequence_length; 
                }
                else EoP = 0x1;
              } 
            }
            // reverse direction:
            else {
              _clk_cnt--; 
              if (reset)  
                _clk_cnt = sequence_length;
              else if (_clk_cnt <= 0) {
                // end of sequence ? 
                if (sequence_count == 0x0) {
                  chords_direction_ = true;
                  _clk_cnt = 0x0; 
                }
                else EoP = -0x1;
              } 
            }
          }
          break;
          case CHORDS_PENDULUM2:
          {
            if (chords_direction_) {

              if (!chord_repeat_)
                _clk_cnt++;
              chord_repeat_ = false;
               
              if (reset)
                _clk_cnt = 0x0;
              else if (_clk_cnt >= sequence_length) {
                // end of sequence ? 
                if (sequence_count >= sequence_max) {
                  chords_direction_ = false;
                  _clk_cnt = sequence_length;  
                  chord_repeat_ = true; // repeat last step
                }
                else EoP = 0x1;  
              }
            }
            // reverse direction:
            else {
              
              if (!chord_repeat_)
                _clk_cnt--; 
              chord_repeat_ = false;
              
              if (reset)  
                _clk_cnt = sequence_length;
              else if (_clk_cnt <= 0x0) {
                // end of sequence ? 
                if (sequence_count == 0x0) {
                  chords_direction_ = true;
                  _clk_cnt = 0x0; 
                  chord_repeat_ = true; // repeat first step
                }
                else EoP = -0x1;  
              }
            }
          }
          break;
          case CHORDS_RANDOM:
          _clk_cnt = random(sequence_length + 0x1);
          if (reset)
            _clk_cnt = 0x0;
          // jump to next sequence if we happen to hit the last note:  
          else if (_clk_cnt >= sequence_length)
            EoP = random(0x2);  
          break;
          default:
          break;
        }
        active_chord_ = _clk_cnt;
        return EoP;
  }

  
  inline void Update(uint32_t triggers) {

    bool triggered = triggers & DIGITAL_INPUT_MASK(0x0);

    trigger_delay_.Update();
    if (triggered)
      trigger_delay_.Push(OC::trigger_delay_ticks[get_trigger_delay()]);
    triggered = trigger_delay_.triggered();
           
    int32_t sample_a = last_sample_;
    int32_t temp_sample = 0;

    if (triggered) {
        
      int32_t pitch, cv_source, transpose, octave, root, mask_rotate;
      int8_t num_progression, num_progression_cv, num_chords, num_chords_cv, progression_max, progression_cnt, playmode, reset;
      
      cv_source = get_cv_source();
      transpose = get_transpose();
      octave = get_octave();
      root = get_root();
      num_progression = get_progression();
      progression_max = 0;
      progression_cnt = 0;
      num_progression_cv = 0;
      num_chords = 0;
      num_chords_cv = 0;
      reset = 0;
      mask_rotate = 0;
      playmode = get_playmode();

      // update mask?
      if (get_mask_cv()) {
        mask_rotate = (OC::ADC::value(static_cast<ADC_CHANNEL>(get_mask_cv() - 0x1)) + 127) >> 8;
      }
              
      update_scale(force_update_, mask_rotate);
      
      if (num_progression != progression_last_ || playmode != playmode_last_) {
        // reset progression:
        progression_cnt_ = 0x0;
        active_progression_ = num_progression;
      }
      playmode_last_ = playmode;
      progression_last_ = num_progression;

      if (get_progression_cv()) {
        num_progression_cv = num_progression += (OC::ADC::value(static_cast<ADC_CHANNEL>(get_progression_cv() - 1)) + 255) >> 9;
        CONSTRAIN(num_progression, 0, OC::Chords::NUM_CHORD_PROGRESSIONS - 0x1);
      }

      if (get_num_chords_cv()) 
        num_chords_cv = (OC::ADC::value(static_cast<ADC_CHANNEL>(get_num_chords_cv() - 1)) + 255) >> 9;

      switch (playmode) {
        
          case _NONE:
            active_progression_ = num_progression;
          break;
          case _SEQ1:
          case _SEQ2:
          case _SEQ3:
          {
              progression_max = playmode;
              
              if (progression_EoP_) {
                
                // increment progression #
                progression_cnt_ += progression_EoP_;
                // reset progression #
                progression_cnt_ = progression_cnt_ > progression_max ? 0x0 : progression_cnt_;
                // update progression 
                active_progression_ = num_progression + progression_cnt_;
                // wrap around:
                if (active_progression_ >= OC::Chords::NUM_CHORD_PROGRESSIONS)
                    active_progression_ -= OC::Chords::NUM_CHORD_PROGRESSIONS;
                // reset    
                _clock(get_num_chords(active_progression_), 0x0, progression_max, true); 
                reset = true;    
              }
              else if (num_progression_cv)  {
                active_progression_ += num_progression_cv;
                CONSTRAIN(active_progression_, 0, OC::Chords::NUM_CHORD_PROGRESSIONS - 0x1);
              }
              progression_cnt = progression_cnt_;
          }
          break;
          case _TR1:
          case _TR2:
          case _TR3:
          {
            // get trigger
            uint8_t _progression_advance_trig = digitalReadFast(TR3);
            progression_max = playmode - _SEQ3;
            
            if (_progression_advance_trig  < progression_advance_last_) {
              // increment progression #
              progression_cnt_++;
              // reset progression #
              progression_cnt_ = progression_cnt_ > progression_max ? 0x0 : progression_cnt_;
              // update progression 
              active_progression_ = num_progression + progression_cnt_;
              // + reset 
              reset = true;
              // wrap around:
              if (active_progression_ >= OC::Chords::NUM_CHORD_PROGRESSIONS)
                  active_progression_ -= OC::Chords::NUM_CHORD_PROGRESSIONS;
            }
            else if (num_progression_cv)  {
                active_progression_ += num_progression_cv;
                CONSTRAIN(active_progression_, 0, OC::Chords::NUM_CHORD_PROGRESSIONS - 0x1);
            }
            progression_advance_last_ = _progression_advance_trig;
            progression_max = 0x0; 
          }
          break;
          case _SH1:
          case _SH2:
          case _SH3:
          case _SH4:
          {
             // SH?
             uint8_t _progression_advance_trig = digitalReadFast(TR3);
             if (_progression_advance_trig  < progression_advance_last_) {
              
               num_chords = get_num_chords(num_progression) + num_chords_cv;
               if (num_chords_cv)
                  CONSTRAIN(num_chords, 0, OC::Chords::NUM_CHORDS - 0x1);         
               // length changed? 
               if (num_chords_last_ != num_chords) 
                  update_inputmap(num_chords + 0x1, 0x0); 
               // store values:  
               num_chords_last_ = num_chords;    
               active_progression_ = num_progression;
               // process input: 
               active_chord_ = input_map_.Process(OC::ADC::value(static_cast<ADC_CHANNEL>(playmode - _SH1)));
             }
             progression_advance_last_ = _progression_advance_trig;
          }
          break;
          case _CV1:
          case _CV2:
          case _CV3:
          case _CV4:
          {
             num_chords = get_num_chords(num_progression) + num_chords_cv;
             if (num_chords_cv) 
                CONSTRAIN(num_chords, 0, OC::Chords::NUM_CHORDS - 0x1);       
             // length changed ? 
             if (num_chords_last_ != num_chords) 
                update_inputmap(num_chords + 0x1, 0x0); 
             // store values:  
             num_chords_last_ = num_chords;    
             active_progression_ = num_progression;
             // process input: 
             active_chord_ = input_map_.Process(OC::ADC::value(static_cast<ADC_CHANNEL>(playmode - _CV1)));
          }
          break;
          default:
          break;
      }

      num_progression = active_progression_;

      if (playmode < _SH1) {
        // next chord via trigger?
        uint8_t _advance_trig = get_chords_trigger_source();
        
        if (_advance_trig == CHORDS_ADVANCE_TRIGGER_SOURCE_TR2) 
          _advance_trig = digitalReadFast(TR2);
        else if (triggered) {
          _advance_trig = 0x0;
          chord_advance_last_ = 0x1;
        }
  
        num_chords = get_num_chords(num_progression) + num_chords_cv;
        if (num_chords_cv) 
            CONSTRAIN(num_chords, 0, OC::Chords::NUM_CHORDS - 0x1);
             
        CONSTRAIN(active_chord_, 0x0, num_chords);
        
        if (num_chords && (_advance_trig < chord_advance_last_)) 
          progression_EoP_ = _clock(num_chords, progression_cnt, progression_max, reset); 
        chord_advance_last_ = _advance_trig;
      } 

      display_num_chords_ = num_chords;
      // active chord:
      OC::Chord *active_chord = &OC::user_chords[active_chord_ + num_progression * OC::Chords::NUM_CHORDS];
      
      int8_t _base_note = active_chord->base_note;
      int8_t _octave = active_chord->octave;
      int8_t _quality = active_chord->quality;
      int8_t _voicing = active_chord->voicing;
      int8_t _inversion = active_chord->inversion;

      octave += _octave;
      CONSTRAIN(octave, -6, 6);

      if (_base_note) {
        /* 
        *  we don't use the incoming CV pitch value — limit to valid base notes. 
        */
        int8_t _limit = OC::Scales::GetScale(get_scale(DUMMY)).num_notes;
        _base_note = _base_note > _limit ? _limit : _base_note;
        pitch = 0x0;
        transpose += (_base_note - 0x1);
      }     
      else {
        pitch = quantizer_.enabled()
                  ? OC::ADC::raw_pitch_value(static_cast<ADC_CHANNEL>(cv_source))
                  : OC::ADC::pitch_value(static_cast<ADC_CHANNEL>(cv_source));
      }
              
      switch (cv_source) {

        case CHORDS_CV_SOURCE_CV1:
        break;
        // todo
        default:
        break;
      }
       
    // S/H mode
      if (get_root_cv()) {
          root += (OC::ADC::value(static_cast<ADC_CHANNEL>(get_root_cv() - 1)) + 127) >> 8;
          CONSTRAIN(root, 0, 15);
      }

      if (get_octave_cv()) {
        octave += (OC::ADC::value(static_cast<ADC_CHANNEL>(get_octave_cv() - 1)) + 255) >> 9;
        CONSTRAIN(octave, -4, 4);
      }
      
      if (get_transpose_cv()) {
        transpose += (OC::ADC::value(static_cast<ADC_CHANNEL>(get_transpose_cv() - 1)) + 63) >> 7;
        CONSTRAIN(transpose, -15, 15);
      }

      if (get_quality_cv()) {
        _quality += (OC::ADC::value(static_cast<ADC_CHANNEL>(get_quality_cv() - 1)) + 255) >> 9;
        CONSTRAIN(_quality, 0,  OC::Chords::CHORDS_QUALITY_LAST - 1);
      }

      if (get_inversion_cv()) {
        _inversion += (OC::ADC::value(static_cast<ADC_CHANNEL>(get_inversion_cv() - 1)) + 511) >> 10;
        CONSTRAIN(_inversion, 0,  OC::Chords::CHORDS_INVERSION_LAST - 1);
      }

      if (get_voicing_cv()) {
        _voicing += (OC::ADC::value(static_cast<ADC_CHANNEL>(get_voicing_cv() - 1)) + 255) >> 9;
        CONSTRAIN(_voicing, 0,  OC::Chords::CHORDS_VOICING_LAST - 1);
      }
      
      int32_t quantized = quantizer_.Process(pitch, root << 7, transpose);
      // main sample, S/H:
      sample_a = temp_sample = OC::DAC::pitch_to_scaled_voltage_dac(DAC_CHANNEL_A, quantized, octave + OC::inversion[_inversion][0], OC::DAC::get_voltage_scaling(DAC_CHANNEL_A));
 
      // now derive chords ...
      transpose += OC::qualities[_quality][1];
      int32_t sample_b  = quantizer_.Process(pitch, root << 7, transpose);
      transpose += OC::qualities[_quality][2];
      int32_t sample_c  = quantizer_.Process(pitch, root << 7, transpose);
      transpose += OC::qualities[_quality][3];
      int32_t sample_d  = quantizer_.Process(pitch, root << 7, transpose);

      //todo voicing for root note
      sample_b = OC::DAC::pitch_to_scaled_voltage_dac(DAC_CHANNEL_B, sample_b, octave + OC::voicing[_voicing][1] + OC::inversion[_inversion][1], OC::DAC::get_voltage_scaling(DAC_CHANNEL_B));
      sample_c = OC::DAC::pitch_to_scaled_voltage_dac(DAC_CHANNEL_C, sample_c, octave + OC::voicing[_voicing][2] + OC::inversion[_inversion][2], OC::DAC::get_voltage_scaling(DAC_CHANNEL_C));
      sample_d = OC::DAC::pitch_to_scaled_voltage_dac(DAC_CHANNEL_D, sample_d, octave + OC::voicing[_voicing][3] + OC::inversion[_inversion][3], OC::DAC::get_voltage_scaling(DAC_CHANNEL_D));
      
      OC::DAC::set<DAC_CHANNEL_A>(sample_a);
      OC::DAC::set<DAC_CHANNEL_B>(sample_b);
      OC::DAC::set<DAC_CHANNEL_C>(sample_c);
      OC::DAC::set<DAC_CHANNEL_D>(sample_d);
    }

    bool changed = (last_sample_ != sample_a);
     
    if (changed) {
      MENU_REDRAW = 1;
      last_sample_ = sample_a;
    }

    if (triggered) {
      clock_display_.Update(1, true);
    } else {
      clock_display_.Update(1, false);
    }
  }

  // Wrappers for ScaleEdit
  void scale_changed() {
    force_update_ = true;
  }

  uint16_t get_scale_mask(uint8_t scale_select) const {
    return get_mask();
  }

  void update_scale_mask(uint16_t mask, uint8_t scale_select) {
    apply_value(CHORDS_SETTING_MASK, mask);
    last_mask_ = mask;
    force_update_ = true;
  }

  // Maintain an internal list of currently available settings, since some are
  // dependent on others. It's kind of brute force, but eh, works :) If other
  // apps have a similar need, it can be moved to a common wrapper

  int num_enabled_settings() const {
    return num_enabled_settings_;
  }

  CHORDS_SETTINGS enabled_setting_at(int index) const {
    return enabled_settings_[index];
  }

  void update_enabled_settings() {
 
    CHORDS_SETTINGS *settings = enabled_settings_;

    switch(get_menu_page()) {

      case MENU_PARAMETERS: { 
        
        *settings++ = CHORDS_SETTING_MASK;
        // hide root ?
        if (get_scale(DUMMY) != OC::Scales::SCALE_NONE)  
          *settings++ = CHORDS_SETTING_ROOT;
        else
           *settings++ = CHORDS_SETTING_MORE_DUMMY;

        *settings++ = CHORDS_SETTING_PROGRESSION;
        *settings++ = CHORDS_SETTING_CHORD_EDIT;
        *settings++ = CHORDS_SETTING_PLAYMODES;
        if (get_playmode() < _SH1)
          *settings++ = CHORDS_SETTING_DIRECTION;
        if (get_direction() == CHORDS_BROWNIAN)       
          *settings++ = CHORDS_SETTING_BROWNIAN_PROBABILITY;       
        *settings++ = CHORDS_SETTING_TRANSPOSE;
        *settings++ = CHORDS_SETTING_OCTAVE;
        *settings++ = CHORDS_SETTING_CV_SOURCE;
        *settings++ = CHORDS_SETTING_CHORDS_ADVANCE_TRIGGER_SOURCE;
        *settings++ = CHORDS_SETTING_TRIGGER_DELAY;
      }
      break;
      case MENU_CV_MAPPING: {

        *settings++ = CHORDS_SETTING_MASK_CV;
        // destinations:
        // hide root CV?
        if (get_scale(DUMMY) != OC::Scales::SCALE_NONE)  
          *settings++ = CHORDS_SETTING_ROOT_CV;
        else
           *settings++ = CHORDS_SETTING_MORE_DUMMY;

        *settings++ = CHORDS_SETTING_PROGRESSION_CV; 
        *settings++ = CHORDS_SETTING_CHORD_EDIT; 
        *settings++ = CHORDS_SETTING_NUM_CHORDS_CV;
        if (get_playmode() < _SH1)
          *settings++ = CHORDS_SETTING_DIRECTION_CV; 
        if (get_direction() == CHORDS_BROWNIAN)       
          *settings++ = CHORDS_SETTING_BROWNIAN_CV; 
        *settings++ = CHORDS_SETTING_TRANSPOSE_CV;
        *settings++ = CHORDS_SETTING_OCTAVE_CV;
        *settings++ = CHORDS_SETTING_QUALITY_CV;
        *settings++ = CHORDS_SETTING_INVERSION_CV;
        *settings++ = CHORDS_SETTING_VOICING_CV;
      }
      break;
      default:
      break;
    }
    // end switch
    num_enabled_settings_ = settings - enabled_settings_;
  }
  
  void RenderScreensaver(weegfx::coord_t x) const;
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
